meslane/APRS_Modem/MSP430_code/APRS_Modem/serial.c

/*
 * serial.c
 *
 *  Created on: Apr 11, 2023
 *      Author: merri
 */


#include <serial.h>
#include <msp430.h>
#include <math.h>

#define MCLK_FREQ_MHZ 8

char A0_RX_array[256];
char A1_RX_array[256];

struct data_queue PORTA0_RX_queue = {.data = A0_RX_array,
                                  .head = 0,
                                  .tail = 0,
                                  .MAX_SIZE = 256};

struct data_queue PORTA1_RX_queue = {.data = A1_RX_array,
                                  .head = 0,
                                  .tail = 0,
                                  .MAX_SIZE = 256};

/* debug UART vector */
#pragma vector=USCI_A1_VECTOR
__interrupt void USCI_A1_ISR(void) {
    switch(__even_in_range(UCA1IV,USCI_UART_UCTXCPTIFG)) {
        case USCI_NONE: break;
        case USCI_UART_UCRXIFG: //char RX'd
            push(&PORTA1_RX_queue, UCA1RXBUF);
            break;
        case USCI_UART_UCTXIFG: break;
        case USCI_UART_UCSTTIFG: break;
        case USCI_UART_UCTXCPTIFG: break;
    }
}

/* GPS UART vector */
#pragma vector=USCI_A0_VECTOR
__interrupt void USCI_A0_ISR(void) {
    switch(__even_in_range(UCA0IV,USCI_UART_UCTXCPTIFG)) {
        case USCI_NONE: break;
        case USCI_UART_UCRXIFG:
            push(&PORTA0_RX_queue, UCA0RXBUF);
            break;
        case USCI_UART_UCTXIFG: break;
        case USCI_UART_UCSTTIFG: break;
        case USCI_UART_UCTXCPTIFG: break;
    }
}

/* This function is from the TI MSP430 example code. Things work without it but I'm not taking any chances */
void Software_Trim() {
    unsigned int oldDcoTap = 0xffff;
    unsigned int newDcoTap = 0xffff;
    unsigned int newDcoDelta = 0xffff;
    unsigned int bestDcoDelta = 0xffff;
    unsigned int csCtl0Copy = 0;
    unsigned int csCtl1Copy = 0;
    unsigned int csCtl0Read = 0;
    unsigned int csCtl1Read = 0;
    unsigned int dcoFreqTrim = 3;
    unsigned char endLoop = 0;

    do
    {
        CSCTL0 = 0x100;                         // DCO Tap = 256
        do
        {
            CSCTL7 &= ~DCOFFG;                  // Clear DCO fault flag
        }while (CSCTL7 & DCOFFG);               // Test DCO fault flag

        __delay_cycles((unsigned int)3000 * MCLK_FREQ_MHZ);// Wait FLL lock status (FLLUNLOCK) to be stable
                                                           // Suggest to wait 24 cycles of divided FLL reference clock
        while((CSCTL7 & (FLLUNLOCK0 | FLLUNLOCK1)) && ((CSCTL7 & DCOFFG) == 0));

        csCtl0Read = CSCTL0;                   // Read CSCTL0
        csCtl1Read = CSCTL1;                   // Read CSCTL1

        oldDcoTap = newDcoTap;                 // Record DCOTAP value of last time
        newDcoTap = csCtl0Read & 0x01ff;       // Get DCOTAP value of this time
        dcoFreqTrim = (csCtl1Read & 0x0070)>>4;// Get DCOFTRIM value

        if(newDcoTap < 256)                    // DCOTAP < 256
        {
            newDcoDelta = 256 - newDcoTap;     // Delta value between DCPTAP and 256
            if((oldDcoTap != 0xffff) && (oldDcoTap >= 256)) // DCOTAP cross 256
                endLoop = 1;                   // Stop while loop
            else
            {
                dcoFreqTrim--;
                CSCTL1 = (csCtl1Read & (~DCOFTRIM)) | (dcoFreqTrim<<4);
            }
        }
        else                                   // DCOTAP >= 256
        {
            newDcoDelta = newDcoTap - 256;     // Delta value between DCPTAP and 256
            if(oldDcoTap < 256)                // DCOTAP cross 256
                endLoop = 1;                   // Stop while loop
            else
            {
                dcoFreqTrim++;
                CSCTL1 = (csCtl1Read & (~DCOFTRIM)) | (dcoFreqTrim<<4);
            }
        }

        if(newDcoDelta < bestDcoDelta)         // Record DCOTAP closest to 256
        {
            csCtl0Copy = csCtl0Read;
            csCtl1Copy = csCtl1Read;
            bestDcoDelta = newDcoDelta;
        }

    }while(endLoop == 0);                      // Poll until endLoop == 1

    CSCTL0 = csCtl0Copy;                       // Reload locked DCOTAP
    CSCTL1 = csCtl1Copy;                       // Reload locked DCOFTRIM
    while(CSCTL7 & (FLLUNLOCK0 | FLLUNLOCK1)); // Poll until FLL is locked
}


void init_clock() {
    __bis_SR_register(SCG0);                 // disable FLL
    CSCTL3 |= SELREF__REFOCLK;               // Set REFO as FLL reference source
    CSCTL1 = DCOFTRIMEN_1 | DCOFTRIM0 | DCOFTRIM1 | DCORSEL_3;// DCOFTRIM=3, DCO Range = 8MHz
    CSCTL2 = FLLD_0 + 243;                  // DCODIV = 8MHz
    __delay_cycles(3);
    __bic_SR_register(SCG0);                // enable FLL
    Software_Trim();                        // Software Trim to get the best DCOFTRIM value

    CSCTL4 = SELMS__DCOCLKDIV | SELA__REFOCLK; // set default REFO(~32768Hz) as ACLK source, ACLK = 32768Hz
                                             // default DCODIV as MCLK and SMCLK source
}

/* init UART to a standard baud rate */
void init_UART_UCA1(unsigned long baud) {
    // Configure UART pins
    P4SEL0 |= BIT2 | BIT3; // set 2-UART pin as second function

    // Configure Clock
    UCA1CTLW0 |= UCSWRST;
    UCA1CTLW0 |= UCSSEL__SMCLK;

    switch(baud) {
    case 115200:
        /* 115200 BAUD settings (from user guide):
        * UCOS16 = 1
        * UCBRF = 5
        * UCBRS = 0x55
        * UCA0BR0 = 4
        */
        UCA1BR0 = 4;
        UCA1BR1 = 0x00;
        UCA1MCTLW = 0x5500 | UCOS16 | UCBRF_5;
        break;
    default: //9600 baud
        // Baud Rate calculation
        // 8000000/(16*9600) = 52.083
        // Fractional portion = 0.083
        // User's Guide Table 17-4: UCBRSx = 0x49
        // UCBRFx = int ( (52.083-52)*16) = 1
        UCA1BR0 = 52;                             // 8000000/16/9600
        UCA1BR1 = 0x00;
        UCA1MCTLW = 0x4900 | UCOS16 | UCBRF_1;
        break;
    }

    UCA1CTLW0 &= ~UCSWRST;                    // Initialize eUSCI
    UCA1IE |= UCRXIE;                         // Enable USCI_A1 RX interrupt
}

/* init UART (GPS UART) */
void init_UART_UCA0(unsigned long baud) {
    // Configure UART pins
    P1SEL0 |= BIT6 | BIT7; // set 2-UART pin as second function

    // Configure Clock
    UCA0CTLW0 |= UCSWRST;
    UCA0CTLW0 |= UCSSEL__SMCLK;

    switch(baud) {
    case 115200:
        /* 115200 BAUD settings (from user guide):
        * UCOS16 = 1
        * UCBRF = 5
        * UCBRS = 0x55
        * UCA0BR0 = 4
        */
        UCA0BR0 = 4;
        UCA0BR1 = 0x00;
        UCA0MCTLW = 0x5500 | UCOS16 | UCBRF_5;
        break;
    default: //9600 baud
        // Baud Rate calculation
        // 8000000/(16*9600) = 52.083
        // Fractional portion = 0.083
        // User's Guide Table 17-4: UCBRSx = 0x49
        // UCBRFx = int ( (52.083-52)*16) = 1
        UCA0BR0 = 52;                             // 8000000/16/9600
        UCA0BR1 = 0x00;
        UCA0MCTLW = 0x4900 | UCOS16 | UCBRF_1;
        break;
    }

    UCA0CTLW0 &= ~UCSWRST;                    // Initialize eUSCI
    UCA0IE |= UCRXIE;                         // Enable USCI_A0 RX interrupt
}

void enable_UART_interrupt(enum serial_port port) {
    switch (port) {
    case PORTA0:
        UCA0IE |= UCRXIE;
        break;
    case PORTA1:
        UCA1IE |= UCRXIE;
        break;
    }
}

void disable_UART_interrupt(enum serial_port port) {
    switch (port) {
    case PORTA0:
        UCA0IE &= ~UCRXIE;
        break;
    case PORTA1:
        UCA1IE &= ~UCRXIE;
        break;
    }
}


/* Wait until the TX buffer is empty and load a char to it */
void putchar(char c) {
    /* wait until transmit buffer is ready (THIS LINE IS VERY IMPORTANT AND UART WILL BREAK WITHOUT IT) */
    while ((UCA1IFG & UCTXIFG) == 0);

    /* Transmit data */
    UCA1TXBUF = c;
}

/* Iterate through a string and transmit chars until the null terminator is encountered */
void putchars(char* msg) {
    unsigned int i = 0;
    char c;

    c = msg[i];
    while(c != '\0') {
        putchar(c);
        i++;
        c = msg[i];
    }
}

char waitchar(enum serial_port port) {
    char c = '\0';

    //wait until char in buffer
    switch(port) {
        case PORTA0:
            while(!(UCA0IFG & UCRXIFG));
            c = UCA0RXBUF;
            break;
        case PORTA1:
            while(!(UCA1IFG & UCRXIFG));
            c = UCA1RXBUF;
            break;
        default:
            break;
    }

    return c;
}

void print_dec(const long long data, const unsigned char len) {
    int i;
    for (i = (len-1); i>=0; i--) {
        putchar(((data / pow(10,i)) % 10) + 48);
    }
}

void int_to_str(char* str, const long long data, const unsigned char len) {
    int i;
    unsigned int j = 0;

    for (i = (len-1); i>=0; i--) {
        str[j] = (((data / pow(10,i)) % 10) + 48);
        j++;
    }
    str[j] = '\0';
}

long long str_to_int(char* str) {
    unsigned int i = 0;
    long long output = 0;
    int sign = 1;

    while (str[i] != '\0' && str[i] != '.') {
        output *= 10;

        if (i == 0 && str[i] == '-') { //detect negative sign
            sign = -1;
        } else {
            output += (str[i] - 0x30); //remove ASCII offset
        }

        i++;
    }

    output *= sign;

    return output;
}

void print_binary(long long b, int n) {
    int i;
    for (i = n; i >= 0; i--) {
        if (((b >> i) & 0x01) == 0x01) {
            putchar('1');
        }
        else {
            putchar('0');
        }
    }
}

void print_hex(char h) {
    int i;
    char nibble;
    for (i = 1; i >= 0; i--) {
        nibble = ((h >> (4 * i)) & 0x0F);
        if (nibble < 10) { //decimal number
            putchar(nibble + 48);
        }
        else { //letter
            putchar(nibble + 55);
        }
    }
}

/* queue functions */
unsigned int get_queue_distance(unsigned int bottom, unsigned int top, unsigned int max) {
    if (top >= bottom) {
        return top - bottom;
    }
    else {
        return (max - bottom) + top;
    }
}

void push(struct data_queue* s, char data) {
    s->data[s->head] = data;
    s->head = s->head < (s->MAX_SIZE - 1) ? s->head + 1 : 0;
}

char pop(struct data_queue* s) {
    char temp = 0;

    temp = s->data[s->tail];
    s->tail = s->tail < (s->MAX_SIZE - 1) ? s->tail + 1 : 0;

    return temp;
}

unsigned int queue_len(struct data_queue* s) {
    return get_queue_distance(s->tail, s->head, s->MAX_SIZE);
}

void push_string(struct data_queue* s, char* str) {
    unsigned int i = 0;
    char c;

    c = str[i];
    while(c != '\0') {
        push(s, c);
        i++;
        c = str[i];
    }
}

void push_packet(struct data_queue* s, char* packet, unsigned int len) {
    unsigned int i;

    for(i=0;i<len;i++) {
        push(s, packet[i]);
    }
}

unsigned char queue_to_str(struct data_queue* s, char* str) {
    unsigned int i = 0;

    while (queue_len(s) > 0) {
        str[i] = pop(s);
        i++;
    }

    return i;
}

void clear_queue(struct data_queue* s) {
    s->head = 0;
    s->tail = 0;
}

//return 1 if strings are equal, 0 otherwise
char streq(char* str1, char* str2, unsigned int len) {
    unsigned int i;

    for (i=0;i<len;i++) {
        if (str1[i] != str2[i]) {
            return 0;
        }
    }

    return 1;
}

//copy one string to another
void strcpy(char* dest, char* src, unsigned int len) {
    unsigned int i;

    for (i=0;i<len;i++) {
        dest[i] = src[i];
    }
}

//append one string to another
unsigned int strcat(char* dest, char* src) {
    unsigned int i;
    unsigned int j;

    i = 0;
    while (dest[i] != '\0') {
        i++;
    }

    j = 0;
    while (src[j] != '\0') {
        dest[i] = src[j];
        j++;
        i++;
    }

    dest[i] = '\0';
    i++;

    return i;
}

unsigned int strlen(char* string) {
    unsigned int len = 0;

    while (string[len] != '\0') {
        len++;
    }

    return len;
}

//returns true if substring is in string
char instr(char* main_string, char* substring) {
    unsigned int i;
    unsigned int j;

    unsigned int main_string_len = strlen(main_string);
    unsigned int substring_len = strlen(substring);

    char match;

    for (i = 0; i < (main_string_len + substring_len); i++) {
        match = 1;
        for (j = 0; j < substring_len; j++) {
            if (main_string[i + j] != substring[j]) {
                match = 0;
                break;
            }
        }

        if (match == 1) {
            return 1;
        }
    }

    return 0; //if not found
}

/* print an int as if it were a fixed-point number */
void FXP_print(int f) {
    const long long ref = 5000000;
    unsigned long long decimal = 0;
    int i;

    if (f < 0) { //if signed
        f -= 1;
        f = ~f;
        putchar('-');
    }

    print_dec((f >> 8) & 0x00FF, 3); //integer part

    for (i = 0; i < 8; i++) {
        if ((f >> (7 - i)) & 0x01 == 0x01) {
            decimal += (ref >> i);
        }
    }

    putchar('.');
    print_dec(decimal, 7); //decimal part
}

/* print 2.14 fixed point int */
void FXP_print_2_14(int f) {
    const long long ref = 5000000000000;
    unsigned long long decimal = 0;
    int i;

    if (f < 0) { //if signed
        f -= 1;
        f = ~f;
        putchar('-');
    }

    print_dec((f >> 14) & 0x0003, 1); //integer part

    for (i = 0; i < 14; i++) {
        if ((f >> (13 - i)) & 0x01 == 0x01) {
            decimal += (ref >> i);
        }
    }

    putchar('.');
    print_dec(decimal, 13); //decimal part
}
