meslane/APRS_Modem/MSP430_code/APRS_Modem/math.c

/*
 * math.c
 *
 *  Created on: Apr 11, 2023
 *      Author: merri
 */
#include <msp430.h>
#include <math.h>

const unsigned char sine_LUT[900] = {
    16,16,16,16,16,16,16,16,16,16,17,17,17,17,17,17,17,17,17,18,18,18,18,18,18,18,18,18,19,19,
    19,19,19,19,19,19,19,19,20,20,20,20,20,20,20,20,20,20,21,21,21,21,21,21,21,21,21,22,22,22,
    22,22,22,22,22,22,22,22,23,23,23,23,23,23,23,23,23,23,24,24,24,24,24,24,24,24,24,24,24,25,
    25,25,25,25,25,25,25,25,25,25,25,26,26,26,26,26,26,26,26,26,26,26,26,26,27,27,27,27,27,27,
    27,27,27,27,27,27,27,28,28,28,28,28,28,28,28,28,28,28,28,28,28,28,28,29,29,29,29,29,29,29,
    29,29,29,29,29,29,29,29,29,29,29,29,30,30,30,30,30,30,30,30,30,30,30,30,30,30,30,30,30,30,
    30,30,30,30,30,30,30,30,30,31,31,31,31,31,31,31,31,31,31,31,31,31,31,31,31,31,31,31,31,31,
    31,31,31,31,31,31,31,31,31,31,31,31,31,31,31,31,31,31,31,31,31,31,31,31,31,31,31,31,31,31,
    31,31,31,31,31,31,31,31,31,31,31,31,31,31,31,31,31,31,31,31,31,31,30,30,30,30,30,30,30,30,
    30,30,30,30,30,30,30,30,30,30,30,30,30,30,30,30,30,30,30,29,29,29,29,29,29,29,29,29,29,29,
    29,29,29,29,29,29,29,29,28,28,28,28,28,28,28,28,28,28,28,28,28,28,28,28,27,27,27,27,27,27,
    27,27,27,27,27,27,27,26,26,26,26,26,26,26,26,26,26,26,26,26,25,25,25,25,25,25,25,25,25,25,
    25,25,24,24,24,24,24,24,24,24,24,24,24,23,23,23,23,23,23,23,23,23,23,22,22,22,22,22,22,22,
    22,22,22,22,21,21,21,21,21,21,21,21,21,20,20,20,20,20,20,20,20,20,20,19,19,19,19,19,19,19,
    19,19,19,18,18,18,18,18,18,18,18,18,17,17,17,17,17,17,17,17,17,16,16,16,16,16,16,16,16,16,
    16,15,15,15,15,15,15,15,15,15,14,14,14,14,14,14,14,14,14,13,13,13,13,13,13,13,13,13,12,12,
    12,12,12,12,12,12,12,12,11,11,11,11,11,11,11,11,11,11,10,10,10,10,10,10,10,10,10,9,9,9,
    9,9,9,9,9,9,9,9,8,8,8,8,8,8,8,8,8,8,7,7,7,7,7,7,7,7,7,7,7,6,
    6,6,6,6,6,6,6,6,6,6,6,5,5,5,5,5,5,5,5,5,5,5,5,5,4,4,4,4,4,4,
    4,4,4,4,4,4,4,3,3,3,3,3,3,3,3,3,3,3,3,3,3,3,3,2,2,2,2,2,2,2,
    2,2,2,2,2,2,2,2,2,2,2,2,1,1,1,1,1,1,1,1,1,1,1,1,1,1,1,1,1,1,
    1,1,1,1,1,1,1,1,1,0,0,0,0,0,0,0,0,0,0,0,0,0,0,0,0,0,0,0,0,0,
    0,0,0,0,0,0,0,0,0,0,0,0,0,0,0,0,0,0,0,0,0,0,0,0,0,0,0,0,0,0,
    0,0,0,0,0,0,0,0,0,0,0,0,0,0,0,0,0,0,0,0,0,0,1,1,1,1,1,1,1,1,
    1,1,1,1,1,1,1,1,1,1,1,1,1,1,1,1,1,1,1,2,2,2,2,2,2,2,2,2,2,2,
    2,2,2,2,2,2,2,2,3,3,3,3,3,3,3,3,3,3,3,3,3,3,3,3,4,4,4,4,4,4,
    4,4,4,4,4,4,4,5,5,5,5,5,5,5,5,5,5,5,5,5,6,6,6,6,6,6,6,6,6,6,
    6,6,7,7,7,7,7,7,7,7,7,7,7,8,8,8,8,8,8,8,8,8,8,9,9,9,9,9,9,9,
    9,9,9,9,10,10,10,10,10,10,10,10,10,11,11,11,11,11,11,11,11,11,11,12,12,12,12,12,12,12,
    12,12,12,13,13,13,13,13,13,13,13,13,14,14,14,14,14,14,14,14,14,15,15,15,15,15,15,15,15,15
};

/* power function */
unsigned long long pow(unsigned long long base, unsigned long long exp) {
    unsigned long long result = 1;
    unsigned long long i;

    for(i=0;i<exp;i++) {
        result *= base;
    }

    return result;
}

void set_bit(char* c, const unsigned char n, const unsigned char val) {
    if ((val & 0x01) == 0x01) {
        *c |= (0x01 << n); //set
    }
    else {
        *c &= ~(0x01 << n); //clear
    }
}

char get_bit(char c, const unsigned char n) {
    return (c >> n) & 0x01;
}

unsigned char sine(unsigned int index) {
    return sine_LUT[index];
}

/* multiply two fixed point numbers (DON'T USE) */
int FXP_mul(int a, int b) {
    long result = a * b;
    return (int)(result >> 8);
}

/* fast fixed point multiplication using the hardware multiplier */
int FXP_mul_hardware(int a, int b) {
    MPYS = a; //load operands
    OP2 = b;

    __no_operation(); //let multiplier finish

    return ((RES1 & 0x00FF) << 8) | ((RES0 >> 8) & 0x00FF);
}

/* TODO: implement hardware multiplication for 2.14 fixed point */
/* (should be faster since the result only needs to be shifted by 2 */
/* can tolerate the loss in precision */
int FXP_mul_2_14(int a, int b) {
    MPYS = a;
    OP2 = b;

    __no_operation();

    return (RES1 << 2);
}

/* saturated addition */
int sat_add(int a, int b) {
    return a+b<a ? 32767 : a+b;
}

/* saturated subtraction */
int sat_sub(int a, int b) {
    return a-b>a ? -32767 : a-b;
}
