meslane/APRS_Modem/MSP430_code/APRS_Modem/dsp.h

/*
 * dsp.h
 *
 *  Created on: Apr 11, 2023
 *      Author: merri
 */

#ifndef DSP_H_
#define DSP_H_

#include <serial.h>

extern struct data_queue symbol_queue;
extern char tx_queue_empty;

extern char rx_ready; //PLL has pulsed
extern char rx_bit; //output from sampling

enum DSP_STATE{DSP_TX, DSP_RX};

void init_ADC(const char channel);
unsigned int get_ADC_result(void);
unsigned int ADC_to_millivolts(unsigned int adcval);

void init_resistor_DAC(void);
void set_resistor_DAC(unsigned char val);

void init_PTT(void);
void PTT_on(void);
void PTT_off(void);

void init_DSP_timer(enum DSP_STATE state);
void enable_DSP_timer(void);
void disable_DSP_timer(void);

#endif /* DSP_H_ */
