meslane/APRS_Modem/MSP430_code/APRS_Modem/math.h

/*
 * math.h
 *
 *  Created on: Apr 11, 2023
 *      Author: merri
 */

#ifndef MATH_H_
#define MATH_H_

unsigned long long pow(unsigned long long base, unsigned long long exp);

void set_bit(char* c, const unsigned char n, const unsigned char val);
char get_bit(char c, const unsigned char n);

unsigned char sine(unsigned int index);

int FXP_mul(int a, int b);
int FXP_mul_hardware(int a, int b);
int FXP_mul_2_14(int a, int b);

int sat_add(int a, int b);
int sat_sub(int a, int b);

#endif /* MATH_H_ */
