meslane/APRS_Modem/MSP430_code/APRS_Modem/ui.c

/*
 * ui.c
 *
 *  Created on: Apr 24, 2023
 *      Author: merri
 */
#include <msp430.h>

#include <ui.h>
#include <math.h>
#include <serial.h>
#include <dsp.h>
#include <packet.h>
#include <gps.h>

enum encoder_dir encoder_state = NONE;

char sleep_done = 0;

int GPS_lock = 0;
int TX_ongoing = 0;
char update_display = 0;

char UTC_str[16];
char coord_str[32];
char elev_str[16];

char lat[16];
char lon[16];

const char digipeater_settings[4][16] = {
    "WIDE2-1",
    "WIDE2-2",
    "WIDE1-1,WIDE2-1",
    "WIDE1-1,WIDE2-2"
};

char* digi;

const char map_symbol_strings[NUM_SYMBOLS][16] = {
    "School",
    "Person",
    "Bicycle",
    "Motorcycle",
    "Canoe",
    "Boat",
    "Car",
    "Truck",
    "Train",
    "Small Plane",
    "Large Plane",
    "Helicopter",
    "Balloon"
};

const char map_symbols[NUM_SYMBOLS] = {
    'K',
    '[',
    'b',
    '<',
    'C',
    'Y',
    '>',
    'u',
    '=',
    '\'',
    '^',
    'X',
    'O'
};

unsigned int current_interval;

/* save during power cycles */
#pragma PERSISTENT(BEACON_INTERVAL);
unsigned int BEACON_INTERVAL = 30;

#pragma PERSISTENT(JITTER_INTERVAL);
unsigned int JITTER_INTERVAL = 0;

#pragma PERSISTENT(digi_index)
unsigned char digi_index = 2;

#pragma PERSISTENT(symbol_index)
unsigned char symbol_index = 0;

#pragma PERSISTENT(TX_while_no_lock)
unsigned char TX_while_no_lock = 0;

#pragma PERSISTENT(call)
char call[10] = "W6NXP    ";

#pragma PERSISTENT(dest)
char dest[10] = "APRS     ";

#pragma vector=PORT4_VECTOR
__interrupt void PORT4_ISR(void) {
    if ((P4IFG & 0x10) == 0x10) { //if clock triggered
        if ((P4IN & 0x80) == 0x80) {
            encoder_state = CW;
        } else {
            encoder_state = CCW;
        }
    }
    else { //if button triggered
        encoder_state = BUTTON;
    }

    P4IFG &= ~(0x50); //reset interrupt flags
}


enum encoder_dir get_encoder_state(void) {
    enum encoder_dir temp;
    temp = encoder_state;
    encoder_state = NONE;
    return temp;
}

/* delay ISR */
#pragma vector=TIMER2_B0_VECTOR
__interrupt void TIMER2_B0_VECTOR_ISR (void) {
    TB2CTL |= TBCLR;
    TB2CTL &= ~(0b11 << 4); //stop timer

    TB2CCTL0 &= ~CCIFG; //reset interrupt

    sleep_done = 1;
    //__bic_SR_register_on_exit(LPM3_bits); //exit sleep mode
}

/* slow delay clock, f = 32.768 kHz divded by 8, p = 244.144us*/
void hardware_delay(unsigned int d) { //4 ~= 1ms
    sleep_done = 0;

    TB2CCTL0 = CCIE; //interrupt mode
    TB2CCR0 = d; //trigger value
    TB2CTL = TBSSEL__ACLK | MC__UP | ID_3 | TBCLR; //slow clock, count up, no division, clear at start

    while(sleep_done == 0);
    sleep_done = 0;
    //__bis_SR_register(LPM3_bits | GIE); //sleep until interrupt is triggered
}

void software_delay(unsigned long long d) {
    unsigned long long i;
    for(i=0;i<d;i++);
}

void init_encoder(void) {
    P4DIR &= ~(0x10); //set P4.4 to input
    P4DIR &= ~(0x40); //set P4.6 to input
    P4DIR &= ~(0x80); //set P4.7 to input
    P4REN &= ~(0xD0); //disable pull resistors
    P4IES &= ~(0x10); //trigger clock on rising edge
    P4IES |= (0x40); //trigger button on falling edge
    P4IE |= 0x10; //enable interrupts
    P4IE |= 0x40;
}

void init_LCD(void) {
    /* LCD Pinout:
     * P1.2 = EN (enable)
     * P1.3 = RS (register select)
     * --------
     * P1.4 = D0
     * P5.3 = D1
     * P5.1 = D2
     * P5.0 = D3
     * P5.4 = D4
     * P1.1 = D5
     * P3.5 = D6
     * P3.1 = D7
     */

    P5SEL1 = 0x00; //set port 5 to GPIO

    P1DIR |= 0x1E; //set P1.1-P1.4 to output
    P3DIR |= 0x22; //set P3.3 and P3.5 to output
    P5DIR |= 0x1B; //set P5.0, P5.1, P5.3 and P5.4 to output

    hardware_delay(450); //delay to let LCD settle

    write_LCD(COMMAND, 0x38);
    write_LCD(COMMAND, 0x06);
    write_LCD(COMMAND, 0x0F);
    write_LCD(COMMAND, 0x01);

    hardware_delay(45);
}

void write_LCD(enum LCD_input type, unsigned char data) {
    switch (type) {
    case DATA:
        P1OUT |= 0x08;
        break;
    case COMMAND:
        P1OUT &= ~(0x08);
        break;
    }

    //set parallel bits (I'm sorry)
    set_bit((char*)&P1OUT, 4, (data >> 0) & 0x01);
    set_bit((char*)&P5OUT, 3, (data >> 1) & 0x01);
    set_bit((char*)&P5OUT, 1, (data >> 2) & 0x01);
    set_bit((char*)&P5OUT, 0, (data >> 3) & 0x01);
    set_bit((char*)&P5OUT, 4, (data >> 4) & 0x01);
    set_bit((char*)&P1OUT, 1, (data >> 5) & 0x01);
    set_bit((char*)&P3OUT, 5, (data >> 6) & 0x01);
    set_bit((char*)&P3OUT, 1, (data >> 7) & 0x01);

    P1OUT |= 0x04;
    hardware_delay(1);
    P1OUT &= ~(0x04);
    hardware_delay(1);
}

void set_LCD_cursor(unsigned char pos) {
    if (pos < 16) {
        write_LCD(COMMAND, 0x80 + pos);
    } else if (pos < 32) {
        write_LCD(COMMAND, 0xB0 + pos);
    }
}

void hide_LCD_cursor(void) {
    write_LCD(COMMAND, 0x0C);
}

void show_LCD_cursor(void) {
    write_LCD(COMMAND, 0x0E);
}

void clear_LCD(void) {
    write_LCD(COMMAND, 0x01);
    hardware_delay(10);
}

void LCD_print(char* str, unsigned char pos) {
    unsigned char i=0;

    while(str[i] != '\0') {
        set_LCD_cursor(pos);
        write_LCD(DATA, str[i]);
        i++;
        pos++;
    }
}

/* enable/disable writing to FRAM */
void enable_FRAM_write(const char enable) {
    switch(enable) {
    case FRAM_WRITE_ENABLE:
        SYSCFG0 = FRWPPW | DFWP; //enable FRAM write
        break;
    case FRAM_WRITE_DISABLE:
        SYSCFG0 = FRWPPW | PFWP | DFWP; //disable FRAM write
        break;
    default:
        break;
    }
}

char modify_value(unsigned int* val, unsigned char digits, enum encoder_dir encoder_state, enum cursor_mode* mode, char* cursor_ptr) {
    char update = 0;

    if (encoder_state == CW) {
        if (*mode == MOVE && *cursor_ptr < 15) {
            *cursor_ptr += 1;
            set_LCD_cursor(*cursor_ptr);
        } else if (*mode == MODIFY) { //modify
            enable_FRAM_write(FRAM_WRITE_ENABLE);
            *val += pow(10, (digits-1)-*cursor_ptr);
            enable_FRAM_write(FRAM_WRITE_DISABLE);
            update = 1;
        }
    }
    else if (encoder_state == CCW) {
        if (*mode == MOVE && *cursor_ptr > 0) {
            *cursor_ptr -= 1;
            set_LCD_cursor(*cursor_ptr);
        } else if (*mode == MODIFY) {
            enable_FRAM_write(FRAM_WRITE_ENABLE);
            *val -= pow(10, (digits-1)-*cursor_ptr);
            enable_FRAM_write(FRAM_WRITE_DISABLE);
            update = 1;
        }
    }
    else if (encoder_state == BUTTON && *cursor_ptr < digits) {
        if (*mode == MODIFY) {
            *mode = MOVE;
        } else if (*mode == MOVE) {
            *mode = MODIFY;
        }
        update = 1;
    }

    return update;
}

char modify_call(char* callsign, enum encoder_dir encoder_state, enum cursor_mode* mode, char* cursor_ptr) {
    char update = 0;

    if (encoder_state == CW) {
        if (*mode == MOVE && *cursor_ptr < 15) {
            *cursor_ptr += 1;
            set_LCD_cursor(*cursor_ptr);
        } else if (*mode == MODIFY) { //modify
            if (callsign[*cursor_ptr] < 0x5A) { //must be valid char
                enable_FRAM_write(FRAM_WRITE_ENABLE);
                callsign[*cursor_ptr]++;
                enable_FRAM_write(FRAM_WRITE_DISABLE);
            }
            update = 1;
        }
    }
    else if (encoder_state == CCW) {
        if (*mode == MOVE && *cursor_ptr > 0) {
            *cursor_ptr -= 1;
            set_LCD_cursor(*cursor_ptr);
        } else if (*mode == MODIFY) {
            if (callsign[*cursor_ptr] > 0x20) { //must be valid char
                enable_FRAM_write(FRAM_WRITE_ENABLE);
                callsign[*cursor_ptr]--;
                enable_FRAM_write(FRAM_WRITE_DISABLE);
            }
            update = 1;
        }
    }
    else if (encoder_state == BUTTON && *cursor_ptr < 9) {
        if (*mode == MODIFY) {
            *mode = MOVE;
        } else if (*mode == MOVE) {
            *mode = MODIFY;
        }
        update = 1;
    }

    return update;
}

//use ADC noise to add jitter to signal
unsigned int get_next_jitter_period(unsigned int period, unsigned int jitter_setting) {
    long long ADC_sum = 0;
    int sign = 0;
    unsigned int i;
    int jitter;

    for(i=0;i<10;i++) {
        ADC_sum += get_ADC_result();
    }

    for (i=0;i<4;i++) {
        sign += get_ADC_result();
    }

    if (sign % 2 == 0) { //determine if positive or negative
        sign = 1;
    } else {
        sign = -1;
    }

    jitter = sign * (ADC_sum % (jitter_setting + 1));

    if (jitter_setting < period) {
        return (period + jitter);
    } else {
        return period;
    }
}


enum UI_state UI_tick(enum UI_state state) {
    static char menu_ptr = 0;
    static char cursor_ptr = 0;
    static enum cursor_mode mode = MOVE;

    char menu_place[4] = {0};
    enum encoder_dir encoder_state = get_encoder_state();
    char temp[16] = {0};
    int temp_int;

    //transitions
    switch (state) {
    case UI_START:
        digi = (char*)digipeater_settings[digi_index];
        state = INFO;
        break;
    case INFO:
        if (encoder_state == BUTTON) {
            state = MENU;
            menu_ptr = 0;
            update_display = 1;
        }
        break;
    case MENU:
        if (encoder_state == BUTTON) {
            switch(menu_ptr) {
            case 0:
                state = PERIOD;
                show_LCD_cursor();
                break;
            case 1:
                state = JITTER;
                show_LCD_cursor();
                break;
            case 2:
                state = DEST;
                show_LCD_cursor();
                break;
            case 3:
                state = CALL;
                show_LCD_cursor();
                break;
            case 4:
                state = REPEAT;
                cursor_ptr = 15;
                hide_LCD_cursor();
                break;
            case 5:
                state = MESSAGE;
                hide_LCD_cursor();
                break;
            case 6:
                state = TX_SETTING;
                hide_LCD_cursor();
                break;
            case 7:
                state = INFO;
                hide_LCD_cursor();
                break;
            default:
                break;
            }
            update_display = 1;
        }
        break;
    case PERIOD:
    case JITTER:
    case DEST:
    case CALL:
    case REPEAT:
    case MESSAGE:
    case TX_SETTING:
        if (encoder_state == BUTTON && cursor_ptr == 15) { //temp
               state = MENU;
               //menu_ptr = 0;
               update_display = 1;
               hide_LCD_cursor();
        }
        break;
    default:
        state = UI_START;
        break;
    }

    //actions
    switch (state) {
    case INFO:
        if (update_display == 1) {
            clear_LCD();

            if (GPS_lock == 0) {
                LCD_print("NO GPS LOCK", 0);
                LCD_print(UTC_str, 16);
            } else {
                coords_to_display(coord_str, lat, lon);
                LCD_print(elev_str, 9);
                LCD_print(lat, 0);
                LCD_print(lon, 16);
            }

            if (TX_ongoing == 1) {
                LCD_print("TX", 30);
            }
        }
        break;
    case MENU:
        if (encoder_state == CW && menu_ptr < (MENU_SIZE - 1)) {
            menu_ptr++;
            update_display = 1;
        }
        else if (encoder_state == CCW && menu_ptr > 0) {
            menu_ptr--;
            update_display = 1;
        }

        if (update_display == 1) {
            clear_LCD();

            switch (menu_ptr) {
            case 0:
                LCD_print("TX Period", 0);
                break;
            case 1:
                LCD_print("TX Jitter", 0);
                break;
            case 2:
                LCD_print("Dest Call", 0);
                break;
            case 3:
                LCD_print("Src Call", 0);
                break;
            case 4:
                LCD_print("Repeaters", 0);
                break;
            case 5:
                LCD_print("Map Symbol", 0);
                break;
            case 6:
                LCD_print("TX Setting", 0);
                break;
            case 7:
                LCD_print("Go Back", 0);
                break;
            }

            LCD_print("Menu", 16);

            menu_place[0] = (menu_ptr + 1) + 0x30;
            menu_place[1] = '/';
            menu_place[2] = MENU_SIZE + 0x30;
            LCD_print(menu_place, 21);
        }
        break;
    case PERIOD:
        temp_int = modify_value(&BEACON_INTERVAL, 5, encoder_state, &mode, &cursor_ptr);
        update_display += temp_int;

        if (temp_int != 0) { //if modified
            current_interval = get_next_jitter_period(BEACON_INTERVAL,JITTER_INTERVAL);
        }

        if (update_display > 0) {
            clear_LCD();
            int_to_str(temp, BEACON_INTERVAL, 5);
            LCD_print(temp, 0);
            LCD_print("^", 15);
            set_LCD_cursor(cursor_ptr);
        }
        break;
    case JITTER:
        temp_int += modify_value(&JITTER_INTERVAL, 5, encoder_state, &mode, &cursor_ptr);
        update_display += temp_int;

        if (temp_int != 0) {
            current_interval = get_next_jitter_period(BEACON_INTERVAL,JITTER_INTERVAL);
        }

        if (update_display > 0) { //if modified
            clear_LCD();
            int_to_str(temp, JITTER_INTERVAL, 5);
            LCD_print(temp, 0);
            LCD_print("^", 15);
            set_LCD_cursor(cursor_ptr);
        }
        break;
    case DEST:
        update_display += modify_call(dest, encoder_state, &mode, &cursor_ptr);

        if (update_display > 0) {
            clear_LCD();
            LCD_print(dest, 0);
            LCD_print("^", 15);
            set_LCD_cursor(cursor_ptr);
        }
        break;
    case CALL:
        update_display += modify_call(call, encoder_state, &mode, &cursor_ptr);

        if (update_display > 0) {
            clear_LCD();
            LCD_print(call, 0);
            LCD_print("^", 15);
            set_LCD_cursor(cursor_ptr);
        }
        break;
    case REPEAT:
        cursor_ptr=15;
        if (encoder_state == CW) {
            if (digi_index < 3) {
                enable_FRAM_write(FRAM_WRITE_ENABLE);
                digi = (char*)digipeater_settings[++digi_index];
                enable_FRAM_write(FRAM_WRITE_DISABLE);
                update_display = 1;
            }
        }
        else if (encoder_state == CCW) {
            if (digi_index > 0) {
                enable_FRAM_write(FRAM_WRITE_ENABLE);
                digi = (char*)digipeater_settings[--digi_index];
                enable_FRAM_write(FRAM_WRITE_DISABLE);
                update_display = 1;
            }
        }

        if (update_display > 0) {
            clear_LCD();
            LCD_print(digi, 0);
            //LCD_print("^", 15);
            set_LCD_cursor(cursor_ptr);
        }
        break;
    case MESSAGE:
        cursor_ptr=15;
        if (encoder_state == CW) {
            if (symbol_index < (NUM_SYMBOLS - 1)) {
                enable_FRAM_write(FRAM_WRITE_ENABLE);
                symbol_index++;
                enable_FRAM_write(FRAM_WRITE_DISABLE);
                update_display = 1;
            }
        }
        else if (encoder_state == CCW) {
            if (symbol_index > 0) {
                enable_FRAM_write(FRAM_WRITE_ENABLE);
                symbol_index--;
                enable_FRAM_write(FRAM_WRITE_DISABLE);
                update_display = 1;
            }
        }

        if (update_display > 0) {
            clear_LCD();
            LCD_print((char*)map_symbol_strings[symbol_index], 0);
            //LCD_print("^", 15);
            set_LCD_cursor(cursor_ptr);
        }
        break;
    case TX_SETTING:
        cursor_ptr=15;

        if (encoder_state == CW || encoder_state == CCW) {
            enable_FRAM_write(FRAM_WRITE_ENABLE);
            TX_while_no_lock ^= 0x01;
            enable_FRAM_write(FRAM_WRITE_DISABLE);
            update_display = 1;
        }

        if (update_display > 0) {
            clear_LCD();
            if (TX_while_no_lock == 0) {
                LCD_print("TX on lock",0);
            } else {
                LCD_print("TX always ",0);
            }
        }

        break;
    default:
        state = UI_START;
        hide_LCD_cursor();
        break;
    }

    update_display = 0;
    return state;
}

/* state machine function */
enum beacon_state beacon_tick(enum beacon_state state, enum UI_state ui_state) {
    static unsigned long long curr_UTC_secs = 0;
    static unsigned long long prev_UTC_secs = 0;

    char c;
    static char GPS_str[256];
    static struct data_queue GPS_queue = {.data = GPS_str,
                                  .head = 0,
                                  .tail = 0,
                                  .MAX_SIZE = 256};

    char packet[400] = {0};
    unsigned int pkt_len;
    unsigned int i;

    static char payload[128];
    static int fix_status;

    //transitions
    switch(state) {
    case BEACON_START:
        state = NO_LOCK;
        current_interval = BEACON_INTERVAL;
        break;
    case NO_LOCK:
        if (GPS_lock > 0) {
            state = LOCK;
            putchars("GPS LOCK ACQUIRED\n\r");
        }
        else if (((curr_UTC_secs - prev_UTC_secs) >= current_interval || (prev_UTC_secs > curr_UTC_secs)) && ui_state == INFO && TX_while_no_lock == 1) { //transition to TX if allowed
            current_interval = get_next_jitter_period(BEACON_INTERVAL,JITTER_INTERVAL);
            state = START_TX;
            TX_ongoing = 1;
        }
        break;
    case LOCK:
        if (GPS_lock < 1) {
            state = NO_LOCK;
            putchars("GPS LOCK LOST\n\r");
        }
        else if (((curr_UTC_secs - prev_UTC_secs) >= current_interval || (prev_UTC_secs > curr_UTC_secs)) && ui_state == INFO) { //don't transmit if in menu
            current_interval = get_next_jitter_period(BEACON_INTERVAL,JITTER_INTERVAL);
            //print_dec(current_interval, 4);
            //putchars("\n\r");
            state = START_TX;
            TX_ongoing = 1;
        }
        break;
    case START_TX:
        state = TX;
        update_display = 1;
        break;
    case TX:
        if (TX_ongoing == 0) {
            state = LOCK;
            update_display = 1;
        }
        break;
    }

    //actions
    switch(state) {
    case LOCK:
    case NO_LOCK:
        while(queue_len(&PORTA0_RX_queue) > 0) { //grab data from GPS
            c = pop(&PORTA0_RX_queue);
            push(&GPS_queue, c);

            if (c == '\n') { //end of data string
                fix_status = parse_GPGGA_string(&GPS_queue, UTC_str, coord_str, elev_str);
                clear_queue(&GPS_queue);
                if (fix_status != -1) { //if correct string
                    GPS_lock = fix_status;
                    curr_UTC_secs = UTC_seconds(UTC_str);

                    if (GPS_lock == 0) {
                        coord_str[0] = '\0'; //make empty string
                    }

                    putchars("UTC: ");
                    putchars(UTC_str);
                    putchars(" ");
                    putchars("Coords: ");
                    putchars(coord_str);
                    putchars(" ");
                    putchars("Elevation: ");
                    putchars(elev_str);
                    putchars("\n\r");

                    update_display = 1;
                }
            }
        }
        break;
    case START_TX:
        disable_UART_interrupt(PORTA0); //prevent GPS UART from interrupting sampling
        clear_queue(&GPS_queue);

        prev_UTC_secs = curr_UTC_secs;

        for (i=0;i<400;i++) { //clear packet
            packet[i] = 0x00;
        }
        coords_to_APRS_payload(payload, coord_str, elev_str, map_symbols[symbol_index]);

        putchars("Transmitting message: ");
        putchars(dest);
        putchars(" ");
        putchars(call);
        putchars(" ");
        putchars(digi);
        putchars(" ");
        putchars(payload);
        putchars("\n\r");

        //pkt_len = make_AX_25_packet(packet, "APRS", "W6NXP", "WIDE1-1,WIDE2-1", payload, 63, 63);
        pkt_len = make_AX_25_packet(packet, dest, call, digi, payload, 63, 63);
        push_packet(&symbol_queue, packet, pkt_len);
        PTT_on(); //key up
        enable_DSP_timer(); //start transmission
        break;
    case TX:
        if (tx_queue_empty == 1) { //wait till empty
            disable_DSP_timer();
            PTT_off();
            enable_UART_interrupt(PORTA0);
            tx_queue_empty = 0;
            TX_ongoing = 0;

            putchars("Transmission Complete\n\r");
        }
        break;
    default:
        break;
    }

    return state;
}
